NetworkEntropologist/28c-eeprom-programmer/firmware/include/debugging.h

/**
 * EEPROM Programmer Firmware
 * @file debugging.h
 * @brief Debugging utilities for 28Cx EEPROM programmer firmware
 * @details Contains functions for debugging and testing the EEPROM programmer firmware.
 *          This may include functions for testing pin states, timing, and communication with the Python control script.
 *          These functions can be called from the main loop or setup to verify correct operation of the hardware and firmware.
 * @note These functions (w)ere used while debugging the initial release of this firmware and as such is provided as-is, without
 * any further documentation or comments. They may be useful for future debugging and testing, but are not intended for regular 
 * use in the main firmware operation.
 */

#ifndef DEBUGGING_H
#define DEBUGGING_H

void addressTestLoop();
void addressWalkRead();
void quickReadTest(uint16_t startAddress, uint16_t endAddress);
void writeTest(uint16_t startAddress, uint16_t endAddress);
void eraseTest(uint16_t startAddress, uint16_t endAddress);

#endif // DEBUGGING_H
